skr-electronics-lab/flyradar32/include/weather_icons.h

#pragma once
#include <lvgl.h>

// =====================================================================
// FlyRadar32 — Hand-crafted 16x16 Weather Alpha Bitmaps (LVGL 8.3)
// Format: LV_IMG_CF_ALPHA_8BIT (256 bytes per icon)
// Compatible with dynamic recoloring: lv_obj_set_style_img_recolor()
// =====================================================================

// 1. Sun (Clear sky) — circular core with 8 radiant sunbeams
static const uint8_t wx_sun_map[256] = {
    0,   0,   0,   0,   0,   0,  80, 255, 255,  80,   0,   0,   0,   0,   0,   0,
    0,   0,   0,   0,   0,   0,   0, 220, 220,   0,   0,   0,   0,   0,   0,   0,
    0,   0, 180,  60,   0,   0,   0,   0,   0,   0,   0,  60, 180,   0,   0,   0,
    0,   0,  60, 240,   0,   0, 100, 200, 200, 100,   0, 240,  60,   0,   0,   0,
    0,   0,   0,   0,   0, 180, 255, 255, 255, 255, 180,   0,   0,   0,   0,   0,
    0,   0,   0,   0, 180, 255, 255, 255, 255, 255, 255, 180,   0,   0,   0,   0,
   80,   0,   0, 100, 255, 255, 255, 255, 255, 255, 255, 255, 100,   0,   0,  80,
  255, 220,   0, 200, 255, 255, 255, 255, 255, 255, 255, 255, 200,   0, 220, 255,
  255, 220,   0, 200, 255, 255, 255, 255, 255, 255, 255, 255, 200,   0, 220, 255,
   80,   0,   0, 100, 255, 255, 255, 255, 255, 255, 255, 255, 100,   0,   0,  80,
    0,   0,   0,   0, 180, 255, 255, 255, 255, 255, 255, 180,   0,   0,   0,   0,
    0,   0,   0,   0,   0, 180, 255, 255, 255, 255, 180,   0,   0,   0,   0,   0,
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
    {LV_IMG_CF_ALPHA_8BIT, 0, 0, 16, 16},
    256,
    wx_temp_map
};

static const lv_img_dsc_t img_wx_baro = {
    {LV_IMG_CF_ALPHA_8BIT, 0, 0, 16, 16},
    256,
    wx_baro_map
};

static const lv_img_dsc_t img_wx_hum = {
    {LV_IMG_CF_ALPHA_8BIT, 0, 0, 16, 16},
    256,
    wx_hum_map
};
